kubanecxxx/matrix-digital-clock/photos/20150624_203648.jpg

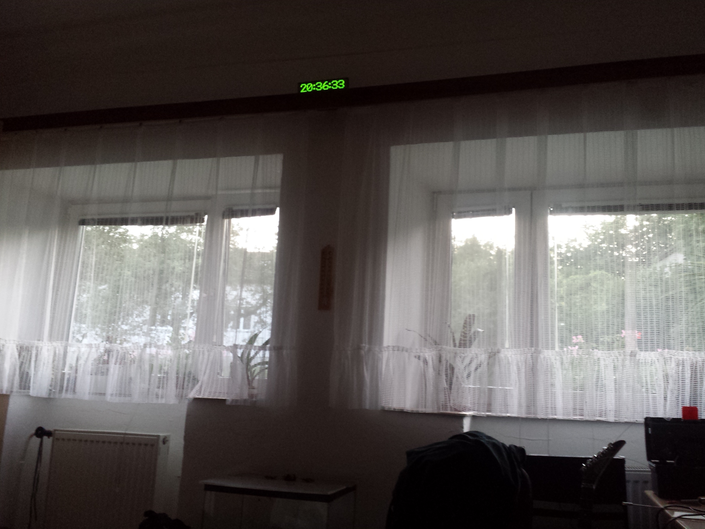
photos/20150624_203648.jpg
